jchadwick/3DM-TabletStand/build/v2/tablet_stand_v2_right_fit_coupon.stl

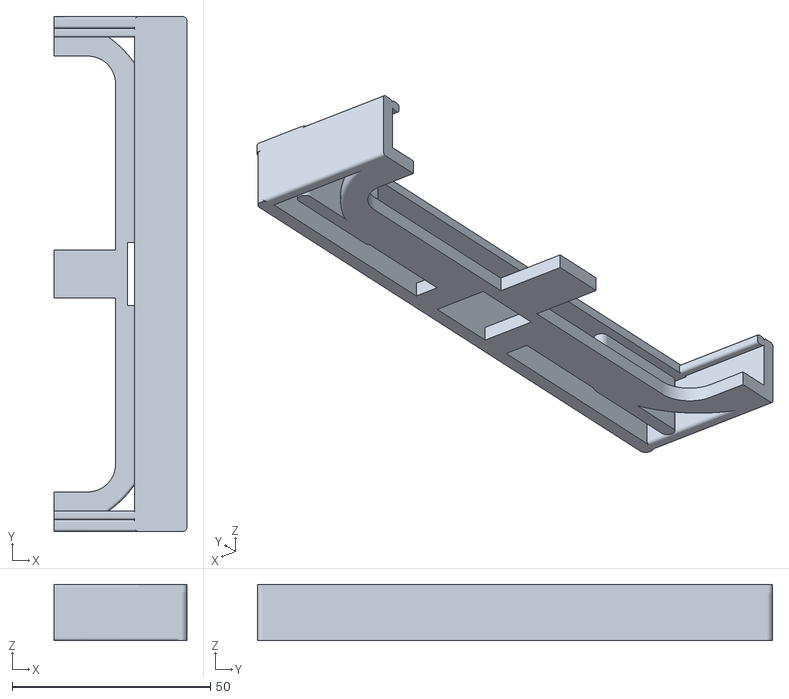
[picture p16: CAD file, 2026-08-25, an earlier design]
build/v2/tablet_stand_v2_right_fit_coupon.stl
33.5 x 130.0 x 14.2
