jchadwick/3DM-TabletStand/build/v2/tablet_stand_v2_end_stop.stl

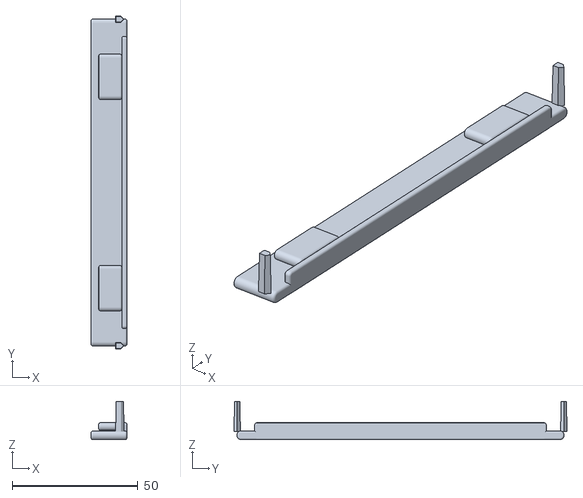
[picture p17: CAD file, 2026-08-25, an earlier design]
build/v2/tablet_stand_v2_end_stop.stl
14.2 x 132.4 x 15.2
