jchadwick/3DM-TabletStand/build/v3/tablet_stand_v3_button_channel.png

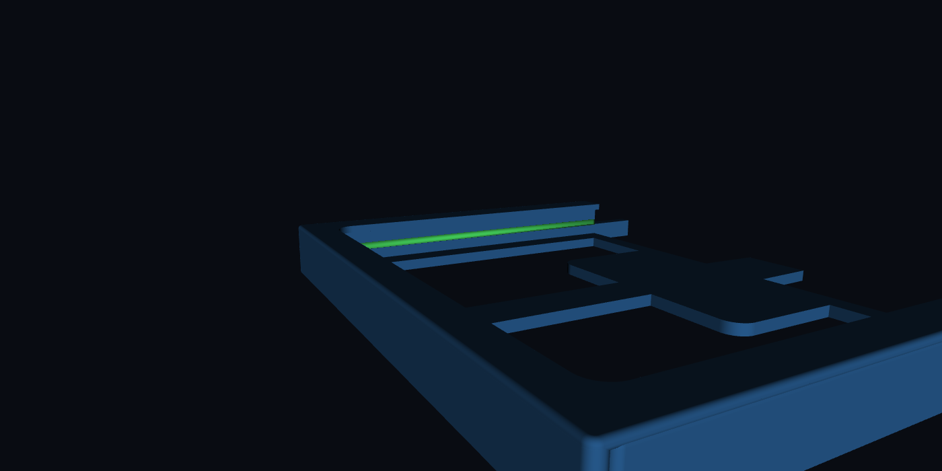
build/v3/tablet_stand_v3_button_channel.png
