jchadwick/3DM-TabletStand/build/v3/tablet_stand_v3_lock_coupon_toolpath.png

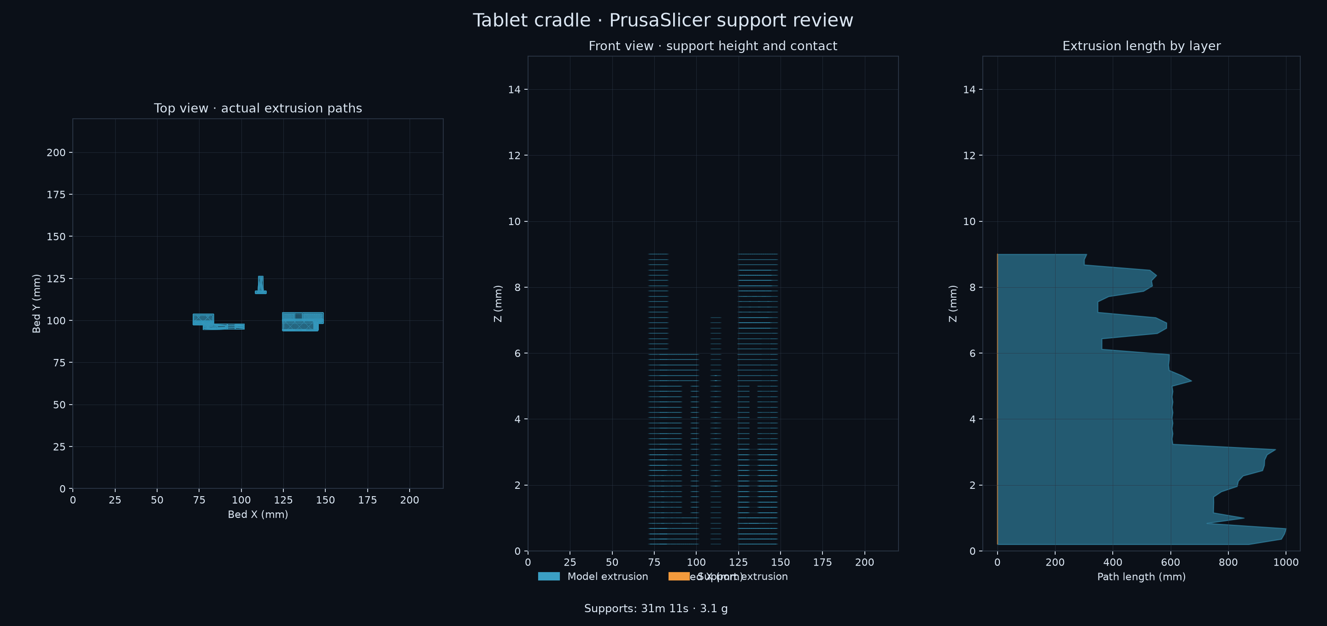
build/v3/tablet_stand_v3_lock_coupon_toolpath.png
