jchadwick/3DM-TabletStand/build/v3/tablet_stand_v3_print_layout.png

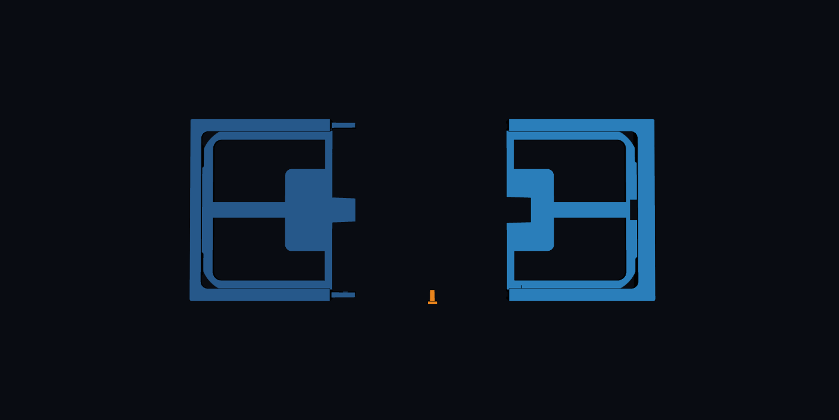
build/v3/tablet_stand_v3_print_layout.png
