jchadwick/3DM-TabletStand/build/v3/tablet_stand_v3_rear_cable.png

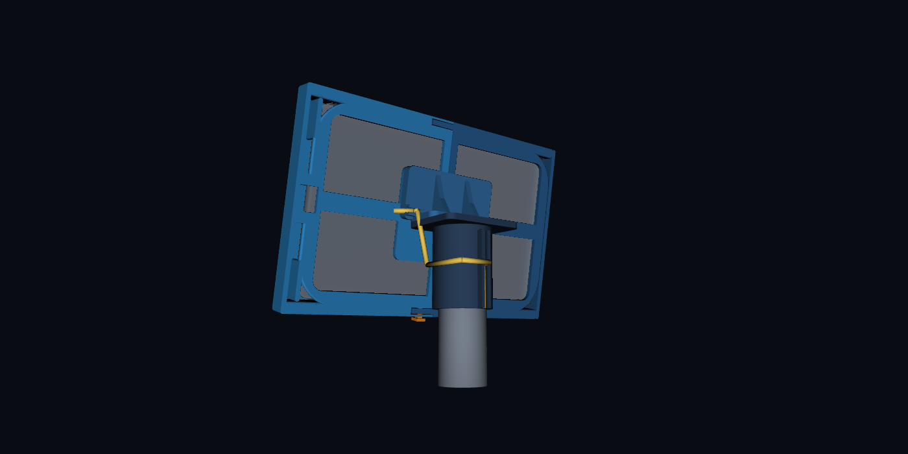
build/v3/tablet_stand_v3_rear_cable.png
