jchadwick/3DM-TabletStand/sphere_test_preview.png

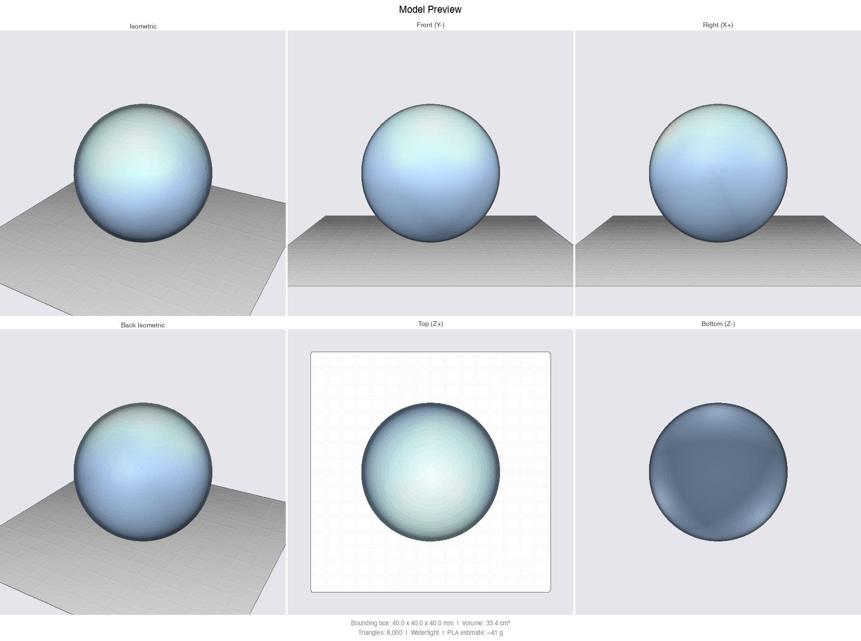
sphere_test_preview.png
